jslawinsk/BrewTempController/Documentation/Arduino Breaboard_bb.png

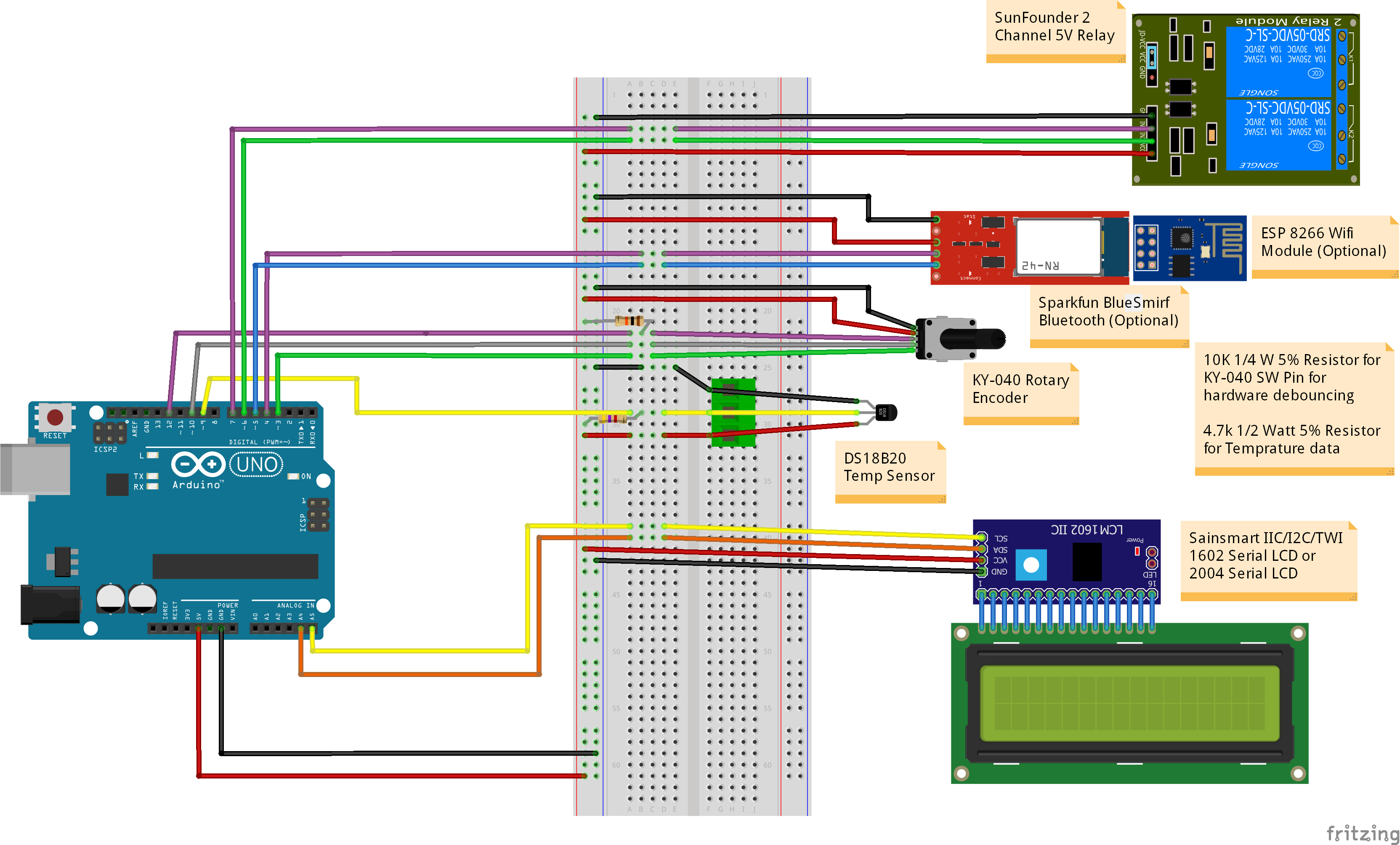
Documentation/Arduino Breaboard_bb.png
