jslawinsk/BrewTempController/Documentation/BrewTempControllerList - Amazon.com_files/41GhcKWBo6L.jpg

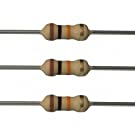
Documentation/BrewTempControllerList - Amazon.com_files/41GhcKWBo6L.jpg
