jslawinsk/BrewTempController/Documentation/BrewTempControllerList - Amazon.com_files/41HxYopw8L.jpg

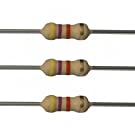
Documentation/BrewTempControllerList - Amazon.com_files/41HxYopw8L.jpg
