jslawinsk/BrewTempController/Documentation/BrewTempControllerList - Amazon.com_files/41iCcWFAtXL.jpg

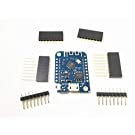
Documentation/BrewTempControllerList - Amazon.com_files/41iCcWFAtXL.jpg
