jslawinsk/BrewTempController/Documentation/BrewTempControllerList - Amazon.com_files/41KROIyuGL.jpg

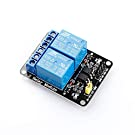
Documentation/BrewTempControllerList - Amazon.com_files/41KROIyuGL.jpg
