jslawinsk/BrewTempController/Documentation/BrewTempControllerList - Amazon.com_files/41mOMHdvSjL.jpg

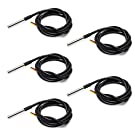
Documentation/BrewTempControllerList - Amazon.com_files/41mOMHdvSjL.jpg
