jslawinsk/BrewTempController/Documentation/BrewTempControllerList - Amazon.com_files/41oJPTlTidL.jpg

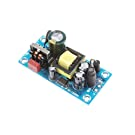
Documentation/BrewTempControllerList - Amazon.com_files/41oJPTlTidL.jpg
