jslawinsk/BrewTempController/Documentation/BrewTempControllerList - Amazon.com_files/41QGQ4MfgxL.jpg

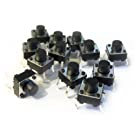
Documentation/BrewTempControllerList - Amazon.com_files/41QGQ4MfgxL.jpg
