jslawinsk/BrewTempController/Documentation/BrewTempControllerList - Amazon.com_files/41rRNfmhAtL.jpg

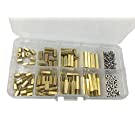
Documentation/BrewTempControllerList - Amazon.com_files/41rRNfmhAtL.jpg
