jslawinsk/BrewTempController/Documentation/BrewTempControllerList - Amazon.com_files/41SsX-RgJxL.jpg

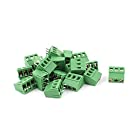
Documentation/BrewTempControllerList - Amazon.com_files/41SsX-RgJxL.jpg
