jslawinsk/BrewTempController/Documentation/BrewTempControllerList - Amazon.com_files/41SU-xj0SRL.jpg

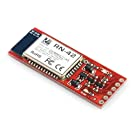
Documentation/BrewTempControllerList - Amazon.com_files/41SU-xj0SRL.jpg
