jslawinsk/BrewTempController/Documentation/BrewTempControllerList - Amazon.com_files/41vGjWuVHDL.jpg

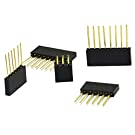
Documentation/BrewTempControllerList - Amazon.com_files/41vGjWuVHDL.jpg
