jslawinsk/BrewTempController/Documentation/BrewTempControllerList - Amazon.com_files/41VzU2BJlWL.jpg

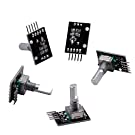
Documentation/BrewTempControllerList - Amazon.com_files/41VzU2BJlWL.jpg
