jslawinsk/BrewTempController/Documentation/BrewTempControllerList - Amazon.com_files/41yAilxTx4L.jpg

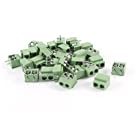
Documentation/BrewTempControllerList - Amazon.com_files/41yAilxTx4L.jpg
