jslawinsk/BrewTempController/Documentation/BrewTempControllerList - Amazon.com_files/51-rR085HrL.jpg

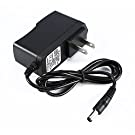
Documentation/BrewTempControllerList - Amazon.com_files/51-rR085HrL.jpg
