jslawinsk/BrewTempController/Documentation/BrewTempControllerList - Amazon.com_files/51BErPVExCL.jpg

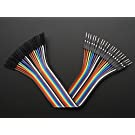
Documentation/BrewTempControllerList - Amazon.com_files/51BErPVExCL.jpg
