jslawinsk/BrewTempController/Documentation/BrewTempControllerList - Amazon.com_files/51CJwrWzvWL.jpg

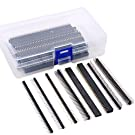
Documentation/BrewTempControllerList - Amazon.com_files/51CJwrWzvWL.jpg
