jslawinsk/BrewTempController/Documentation/BrewTempControllerList - Amazon.com_files/51faMfWgp0L.jpg

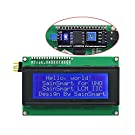
Documentation/BrewTempControllerList - Amazon.com_files/51faMfWgp0L.jpg
