jslawinsk/BrewTempController/Documentation/BrewTempControllerList - Amazon.com_files/51fol0dx7dL.jpg

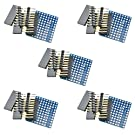
Documentation/BrewTempControllerList - Amazon.com_files/51fol0dx7dL.jpg
