jslawinsk/BrewTempController/Documentation/BrewTempControllerList - Amazon.com_files/51r7ki-1mL.jpg

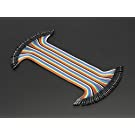
Documentation/BrewTempControllerList - Amazon.com_files/51r7ki-1mL.jpg
