jslawinsk/BrewTempController/Documentation/BrewTempControllerList - Amazon.com_files/51rmayrbsPL.jpg

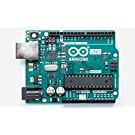
Documentation/BrewTempControllerList - Amazon.com_files/51rmayrbsPL.jpg
