jslawinsk/BrewTempController/Documentation/BrewTempControllerList - Amazon.com_files/51XwerfrSL.jpg

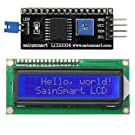
Documentation/BrewTempControllerList - Amazon.com_files/51XwerfrSL.jpg
