jslawinsk/BrewTempController/Documentation/BrewTempControllerList - Amazon.com_files/51YEGr9smYL.jpg

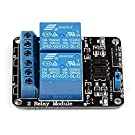
Documentation/BrewTempControllerList - Amazon.com_files/51YEGr9smYL.jpg
