jslawinsk/BrewTempController/Documentation/BrewTempControllerList - Amazon.com_files/51ZcqcF1nAL.jpg

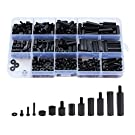
Documentation/BrewTempControllerList - Amazon.com_files/51ZcqcF1nAL.jpg
