jslawinsk/BrewTempController/Documentation/BrewTempControllerList - Amazon.com_files/51zipPJyYcL.jpg

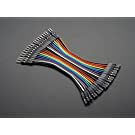
Documentation/BrewTempControllerList - Amazon.com_files/51zipPJyYcL.jpg
