jslawinsk/BrewTempController/Documentation/BrewTempControllerList - Amazon.com_files/61dFtJG7AnL.jpg

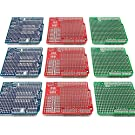
Documentation/BrewTempControllerList - Amazon.com_files/61dFtJG7AnL.jpg
