jslawinsk/BrewTempController/Documentation/BrewTempControllerList - Amazon.com_files/310f4BGjlOL.jpg

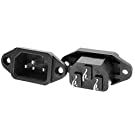
Documentation/BrewTempControllerList - Amazon.com_files/310f4BGjlOL.jpg
