jslawinsk/BrewTempController/Documentation/BrewTempControllerList - Amazon.com_files/510f7v47QIL.jpg

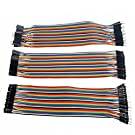
Documentation/BrewTempControllerList - Amazon.com_files/510f7v47QIL.jpg
