jslawinsk/BrewTempController/Documentation/D1Prototype/D1Mini-2.png

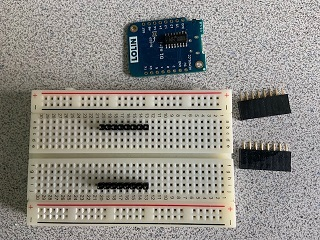
Documentation/D1Prototype/D1Mini-2.png
