jslawinsk/BrewTempController/Documentation/D1Prototype/D1Mini-3.png

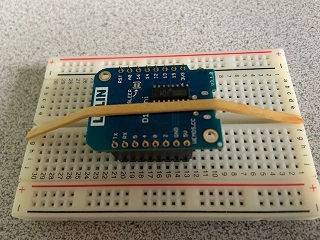
Documentation/D1Prototype/D1Mini-3.png
