jslawinsk/BrewTempController/Documentation/D1Prototype/D1Mini-4.png

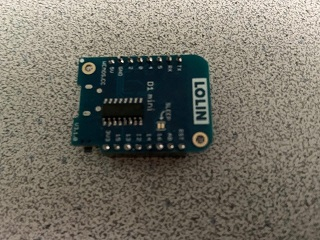
Documentation/D1Prototype/D1Mini-4.png
