jslawinsk/BrewTempController/Documentation/D1Prototype/D1Mini-5.png

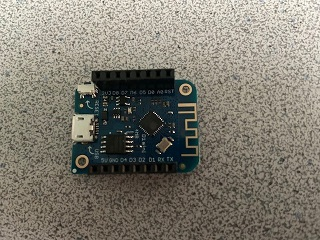
Documentation/D1Prototype/D1Mini-5.png
