jslawinsk/BrewTempController/Documentation/D1Prototype/D1MiniEnclosure1.png

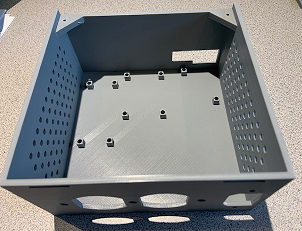
Documentation/D1Prototype/D1MiniEnclosure1.png
