jslawinsk/BrewTempController/Documentation/D1Prototype/D1MiniEnclosure2.png

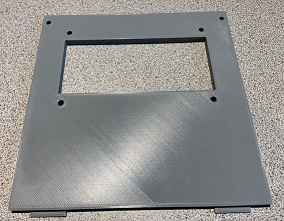
Documentation/D1Prototype/D1MiniEnclosure2.png
