jslawinsk/BrewTempController/Documentation/D1Prototype/D1MiniEnclosure3.png

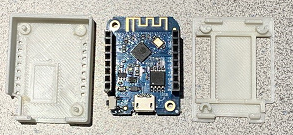
Documentation/D1Prototype/D1MiniEnclosure3.png
