jslawinsk/BrewTempController/Documentation/D1Prototype/D1MiniEnclosure4.png

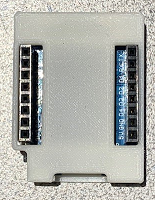
Documentation/D1Prototype/D1MiniEnclosure4.png
