jslawinsk/BrewTempController/Documentation/D1Prototype/D1MiniLCD.png

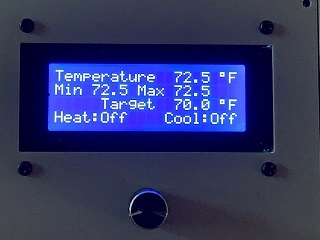
Documentation/D1Prototype/D1MiniLCD.png
