jslawinsk/BrewTempController/Documentation/D1Prototype/D1MiniShield2.png

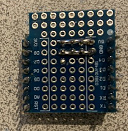
Documentation/D1Prototype/D1MiniShield2.png
