jslawinsk/BrewTempController/Documentation/D1Prototype/D1MiniShield3.png

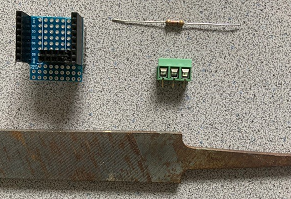
Documentation/D1Prototype/D1MiniShield3.png
