jslawinsk/BrewTempController/Documentation/D1Prototype/D1MiniShield4.png

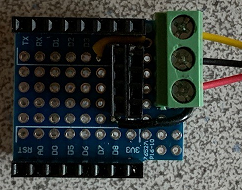
Documentation/D1Prototype/D1MiniShield4.png
