jslawinsk/BrewTempController/Documentation/D1Prototype/D1MiniShield5.png

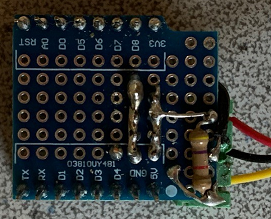
Documentation/D1Prototype/D1MiniShield5.png
