jslawinsk/BrewTempController/Documentation/D1Prototype/D1MiniShield6.png

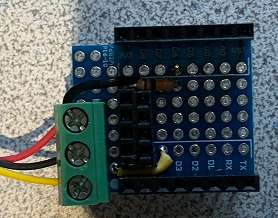
Documentation/D1Prototype/D1MiniShield6.png
