jslawinsk/BrewTempController/Documentation/D1Prototype/D1MiniShield7.png

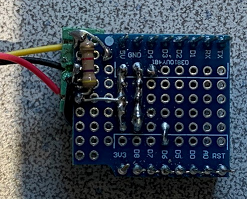
Documentation/D1Prototype/D1MiniShield7.png
