jslawinsk/BrewTempController/Documentation/D1Prototype/D1MiniWireing1.png

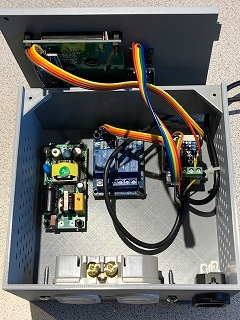
Documentation/D1Prototype/D1MiniWireing1.png
