jslawinsk/BrewTempController/Documentation/D1Prototype/D1MiniWireing2.png

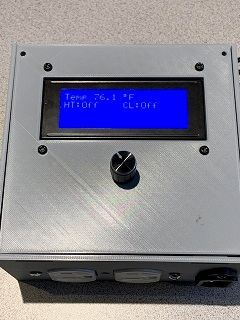
Documentation/D1Prototype/D1MiniWireing2.png
