jslawinsk/BrewTempController/Documentation/LolinD1Mini Breaboard_bb.png

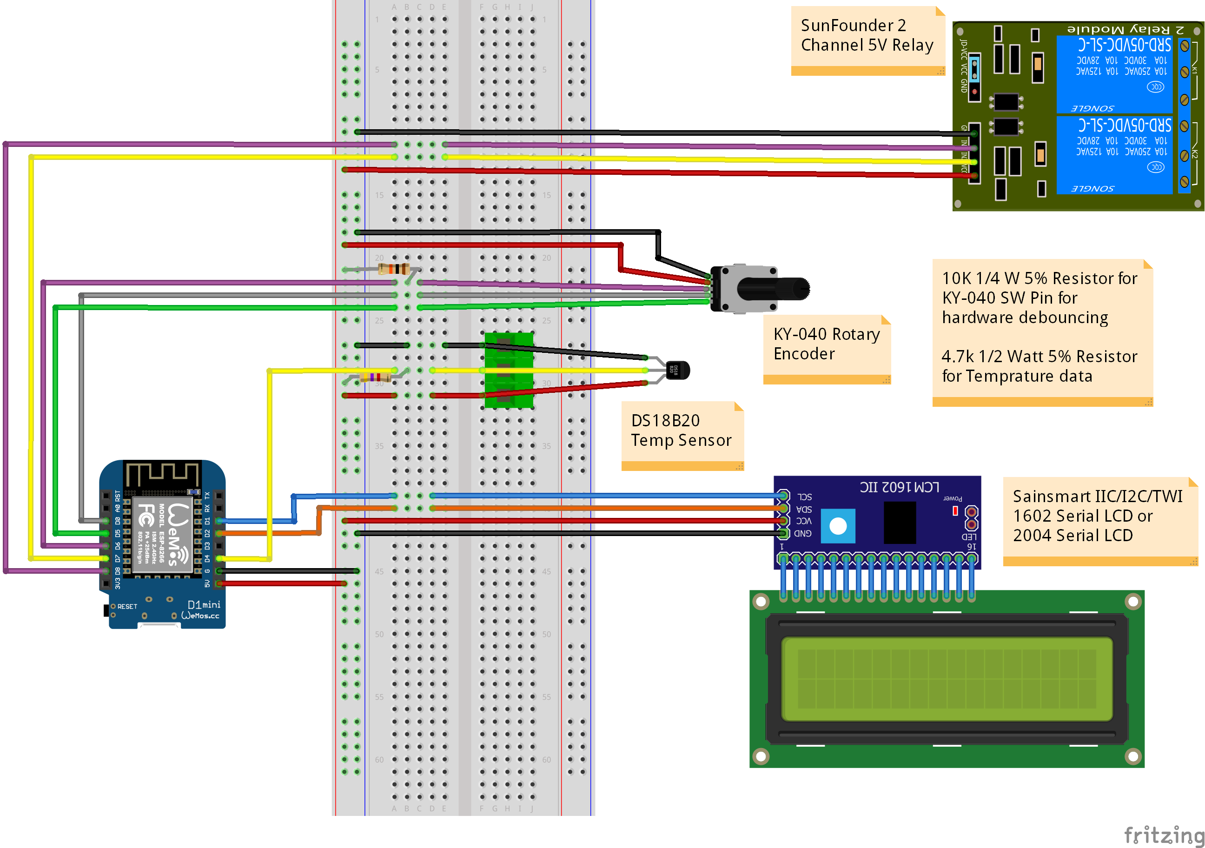
Documentation/LolinD1Mini Breaboard_bb.png
