jslawinsk/BrewTempController/Documentation/LolinD1Mini Shield_bb.png

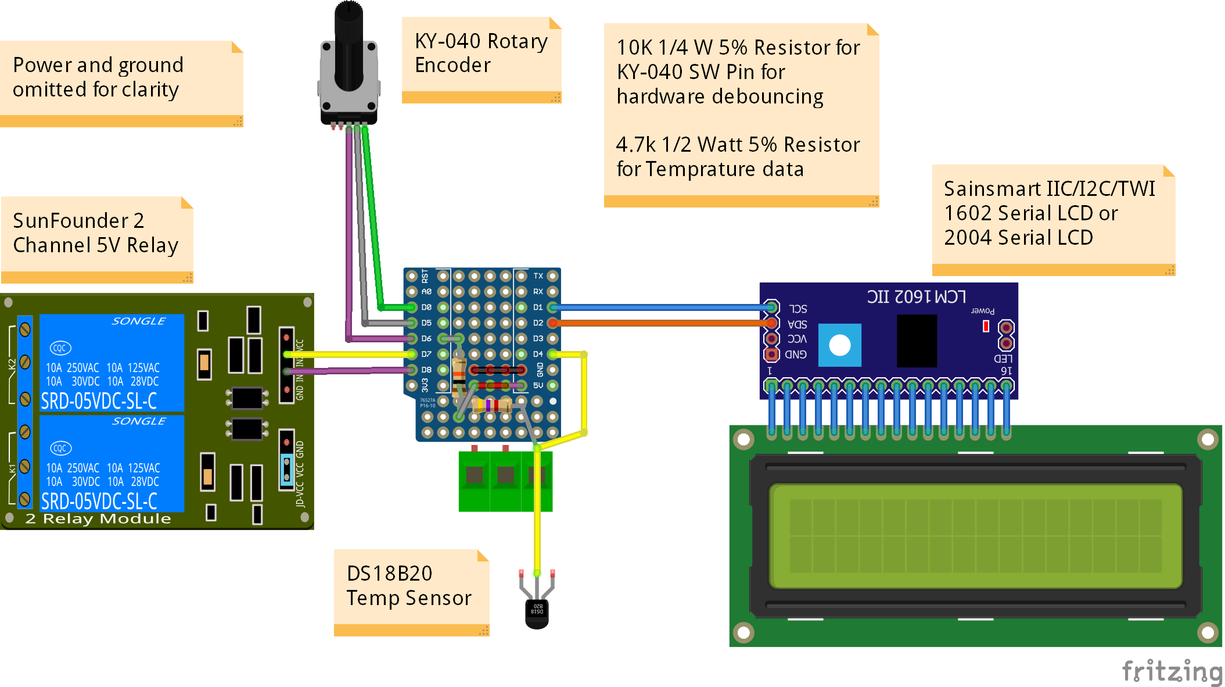
Documentation/LolinD1Mini Shield_bb.png
