jslawinsk/BrewTempController/Documentation/ProtoType/Protype01.png

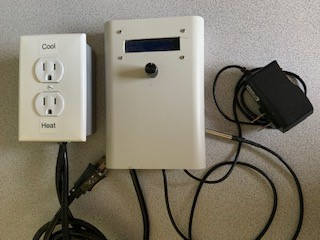
Documentation/ProtoType/Protype01.png
