jslawinsk/BrewTempController/Documentation/ProtoType/Protype02.png

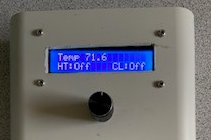
Documentation/ProtoType/Protype02.png
