jslawinsk/BrewTempController/Documentation/ProtoType/Protype04.png

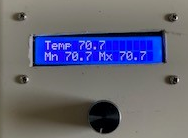
Documentation/ProtoType/Protype04.png
