jslawinsk/BrewTempController/Documentation/ProtoType/Protype06.png

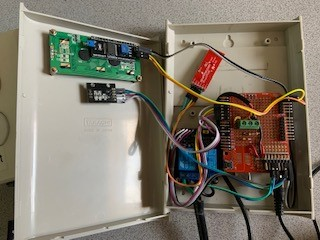
Documentation/ProtoType/Protype06.png
