jslawinsk/BrewTempController/Documentation/ProtoType/Protype07.png

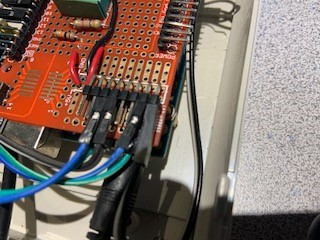
Documentation/ProtoType/Protype07.png
