jslawinsk/BrewTempController/Documentation/ProtoType/Protype08.png

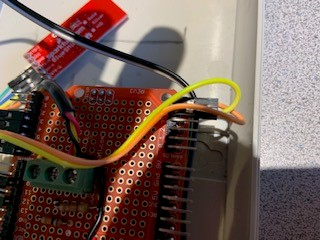
Documentation/ProtoType/Protype08.png
