jslawinsk/BrewTempController/Documentation/ProtoType/Protype09.png

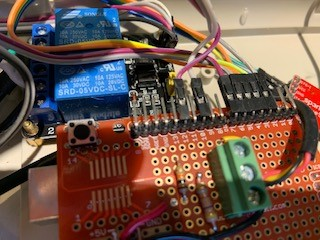
Documentation/ProtoType/Protype09.png
