jslawinsk/BrewTempController/Documentation/ProtoType/Protype10.png

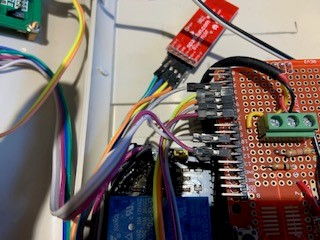
Documentation/ProtoType/Protype10.png
