jslawinsk/BrewTempController/Documentation/ProtoType/Protype11.png

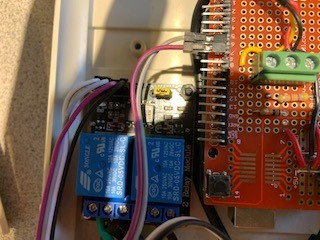
Documentation/ProtoType/Protype11.png
