jslawinsk/BrewTempController/Documentation/ProtoType/Protype14.png

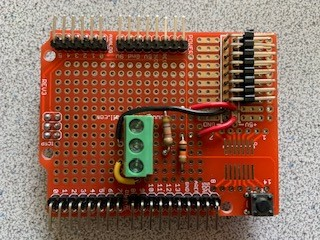
Documentation/ProtoType/Protype14.png
