jslawinsk/BrewTempController/Documentation/ProtoType/Protype17.png

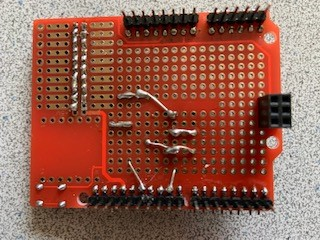
Documentation/ProtoType/Protype17.png
