jslawinsk/BrewTempController/Documentation/Wifi01.png

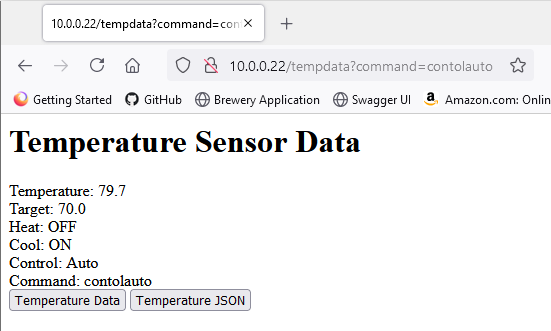
Documentation/Wifi01.png
