jslawinsk/BrewTempController/Documentation/Wifi02.png

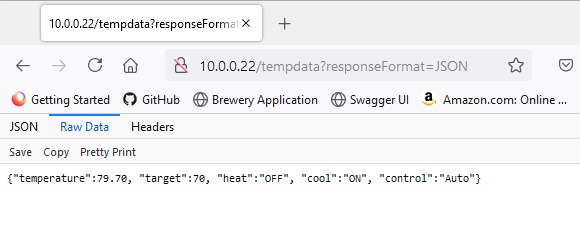
Documentation/Wifi02.png
