jslawinsk/BrewTempController/Documentation/D1Prototype/D1MiniBuild1.png

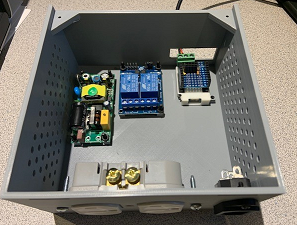
Documentation/D1Prototype/D1MiniBuild1.png
