jslawinsk/BrewTempController/Documentation/D1Prototype/D1MiniBuild2.png

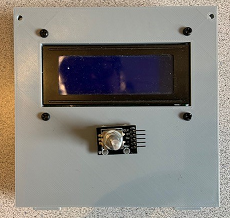
Documentation/D1Prototype/D1MiniBuild2.png
