jslawinsk/BrewTempController/Documentation/D1Prototype/D1MiniBuild3.png

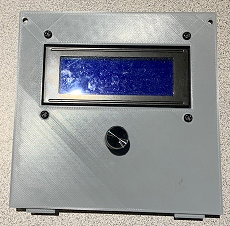
Documentation/D1Prototype/D1MiniBuild3.png
