jslawinsk/BrewTempController/Documentation/D1Prototype/D1MiniBuild4.png

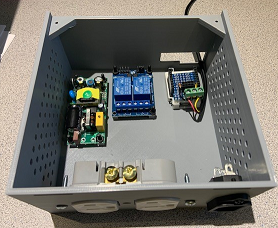
Documentation/D1Prototype/D1MiniBuild4.png
