jslawinsk/BrewTempController/Documentation/D1Prototype/D1MiniBuild5.png

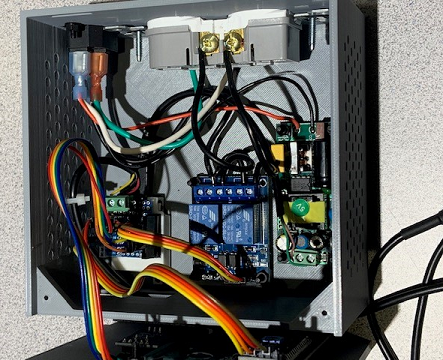
Documentation/D1Prototype/D1MiniBuild5.png
