jslawinsk/BrewTempController/Documentation/D1Prototype/D1MiniBuild6.png

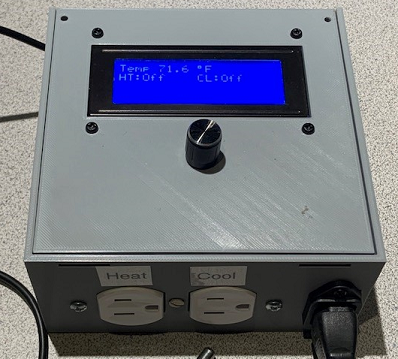
Documentation/D1Prototype/D1MiniBuild6.png
