jslawinsk/BrewTempController/Documentation/DeveloperSetup/Sketch1.png

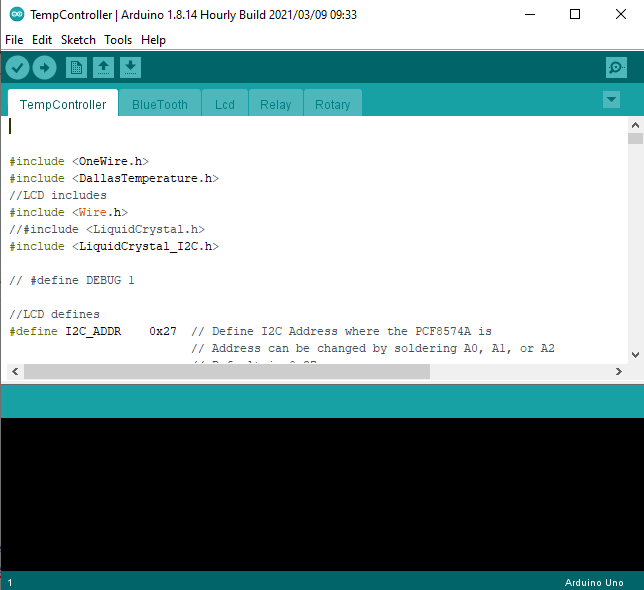
Documentation/DeveloperSetup/Sketch1.png
